dilshan/ntp-clock/resources/netclock-wirelayout/CONTROL-BTN.sch

## KiCad design resources/netclock-wirelayout/CONTROL-BTN.sch (2021-04-27)

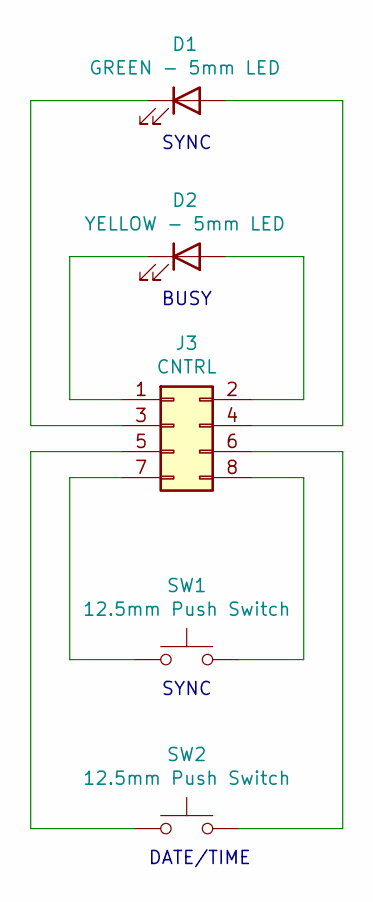
[picture p8: schematic CONTROL-BTN.sch]

Parts:
D1: GREEN - 5mm LED
D2: YELLOW - 5mm LED
J3: CNTRL
SW1, SW2: 12.5mm Push Switch

Connections:
unnamed: D1.1 (K), J3.3
unnamed: D1.2 (A), J3.4
unnamed: D2.1 (K), J3.1
unnamed: D2.2 (A), J3.2
unnamed: J3.5, SW2.1
unnamed: J3.6, SW2.2
unnamed: J3.7, SW1.1
unnamed: J3.8, SW1.2

Notes on the sheet:
BUSY
SYNC
DATE/TIME
