dilshan/ntp-clock/resources/netclock-wirelayout/SSD-LAYOUT.sch

## KiCad design resources/netclock-wirelayout/SSD-LAYOUT.sch (2021-04-27)

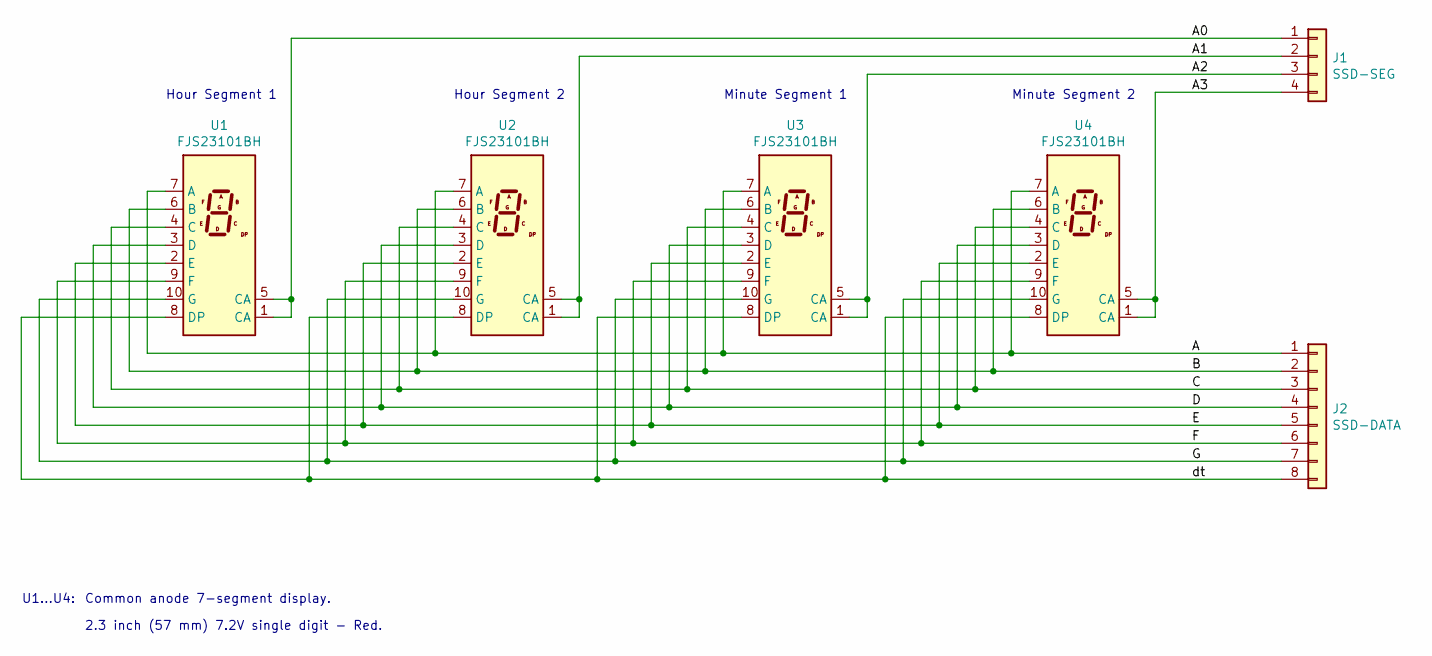
[picture p9: schematic SSD-LAYOUT.sch]

Parts:
J1: SSD-SEG
J2: SSD-DATA
U1, U2, U3, U4: FJS23101BH; SA15-11xxx

Connections:
A: J2.1, U1.7 (A), U2.7 (A), U3.7 (A), U4.7 (A)
A0: J1.1, U1.1 (CA), U1.5 (CA)
A1: J1.2, U2.1 (CA), U2.5 (CA)
A2: J1.3, U3.1 (CA), U3.5 (CA)
A3: J1.4, U4.1 (CA), U4.5 (CA)
B: J2.2, U1.6 (B), U2.6 (B), U3.6 (B), U4.6 (B)
C: J2.3, U1.4 (C), U2.4 (C), U3.4 (C), U4.4 (C)
D: J2.4, U1.3 (D), U2.3 (D), U3.3 (D), U4.3 (D)
E: J2.5, U1.2 (E), U2.2 (E), U3.2 (E), U4.2 (E)
F: J2.6, U1.9 (F), U2.9 (F), U3.9 (F), U4.9 (F)
G: J2.7, U1.10 (G), U2.10 (G), U3.10 (G), U4.10 (G)
dt: J2.8, U1.8 (DP), U2.8 (DP), U3.8 (DP), U4.8 (DP)

Notes on the sheet:
U1...U4:
2.3 inch (57 mm) 7.2V single digit - Red.
Common anode 7-segment display.
Hour Segment 1
Hour Segment 2
Minute Segment 1
Minute Segment 2
